STrRedWolf/ebadge-Arduino/images/IMG_0415.jpg

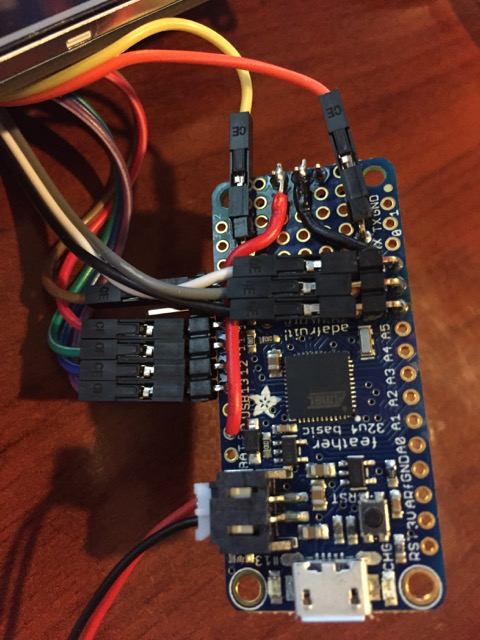
images/IMG_0415.jpg
