STrRedWolf/ebadge-Arduino/images/IMG_0417.jpg

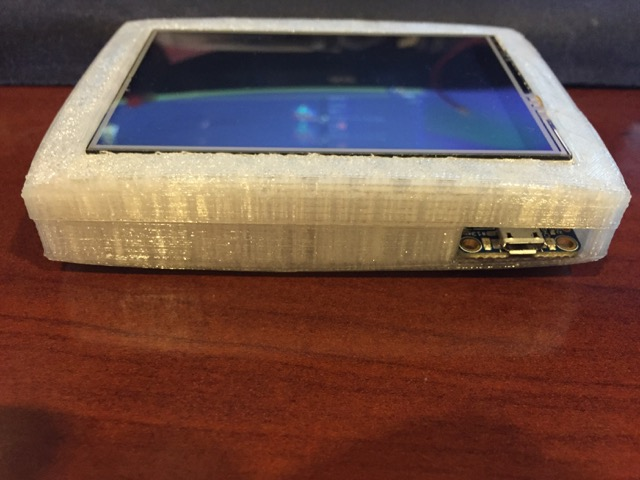
images/IMG_0417.jpg
