STrRedWolf/ebadge-Arduino/images/IMG_0434.jpg

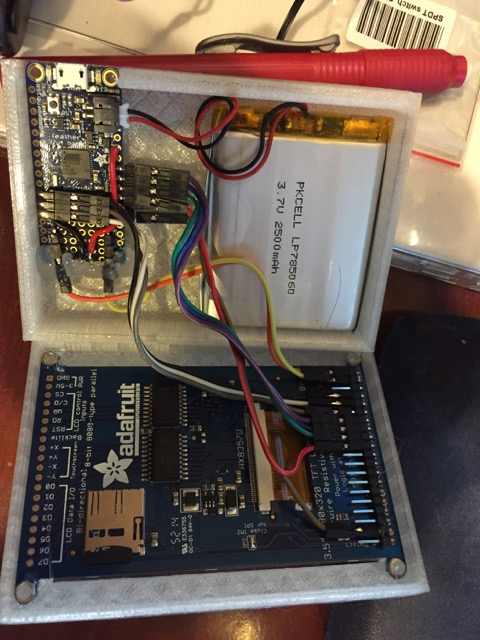
images/IMG_0434.jpg
